punklibrarian/ATtiny_45_and_85_programmer_shield/KiCad/Version 1.2/ATtiny_45_and_85_programmer_shield.sch

## KiCad design KiCad/Version 1.2/ATtiny_45_and_85_programmer_shield.sch (2011-11-27)

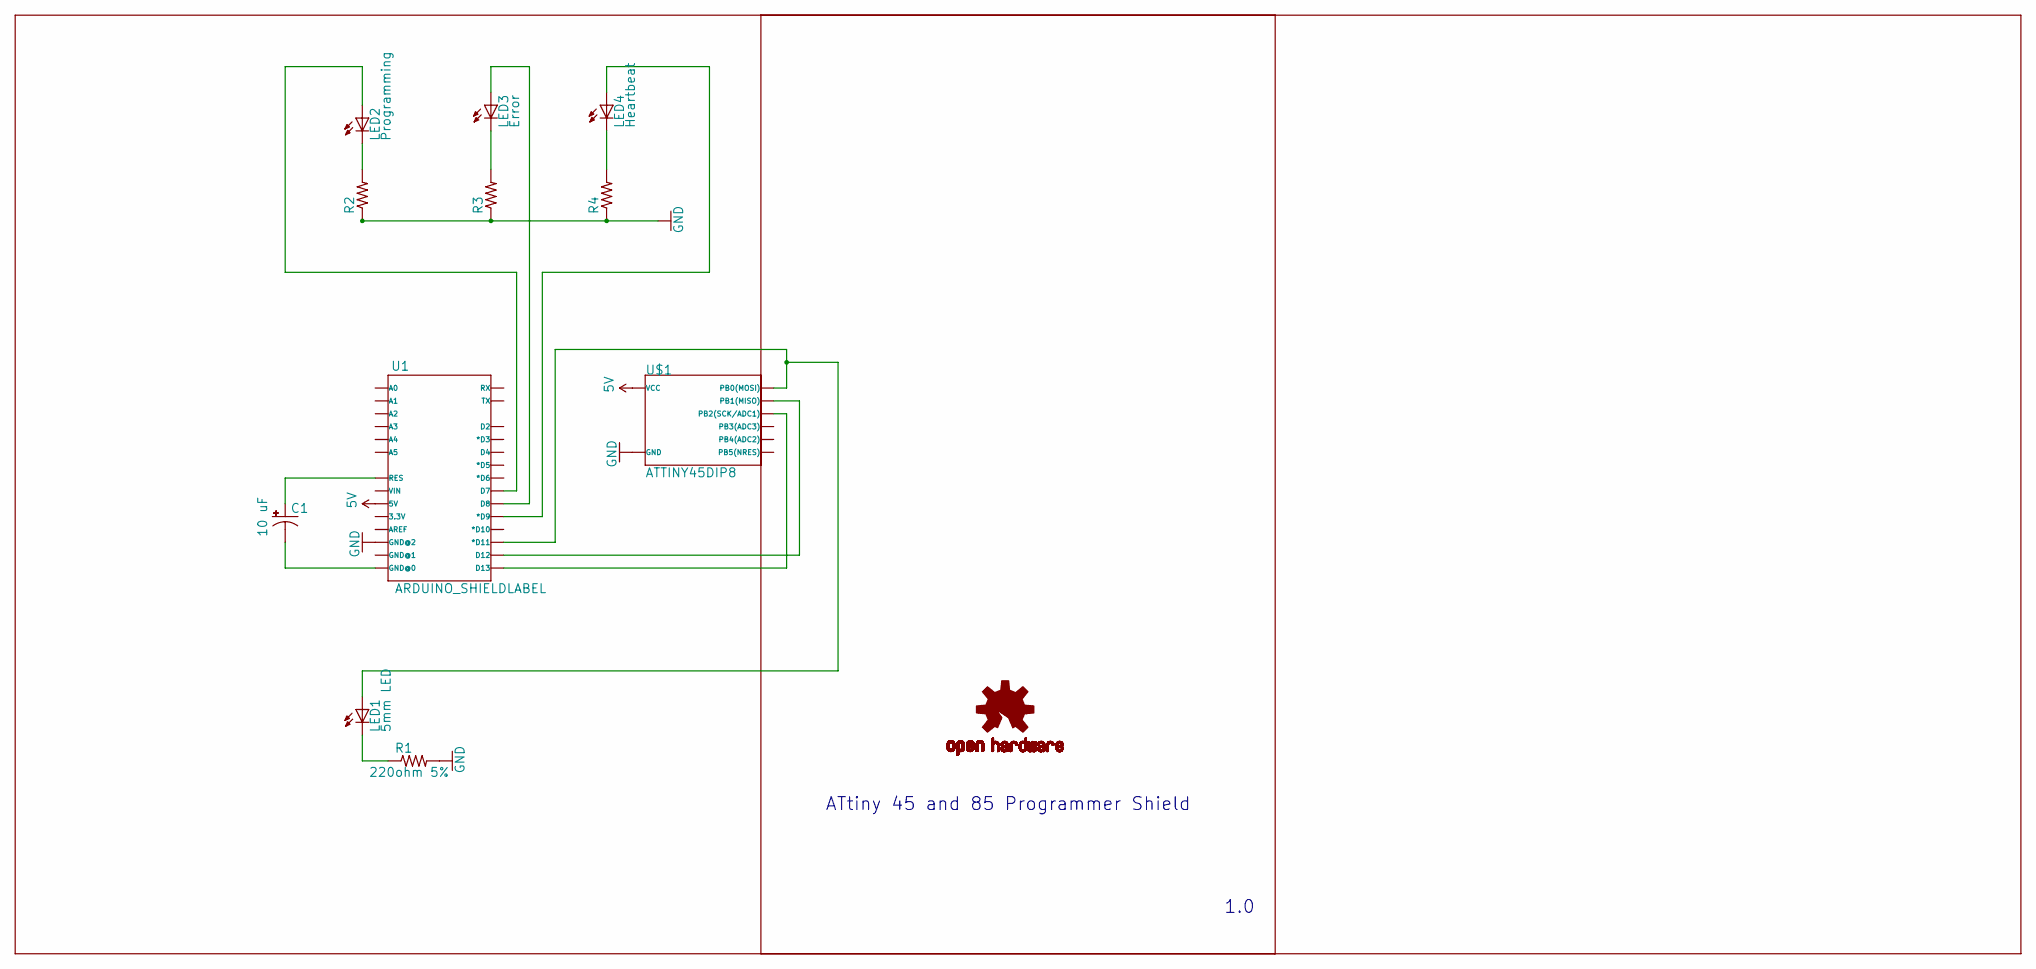
[picture p7: schematic ATtiny_45_and_85_programmer_shield.sch]

Parts:
C1: 10 uF
FRAME1: (no value)
GND1, GND2, GND3, GND4: (no value)
LED1: 5mm LED
LED2: Programming
LED3: Error
LED4: Heartbeat
R1: 220ohm 5%
R2, R3, R4: (no value)
U1: ARDUINO_SHIELDLABEL
U$1: U$1
U$2, U$3, U$4: (no value)

Connections:
unnamed: C1.A (+), U1.RES
unnamed: C1.C (-), U1.GND@0
unnamed: GND1.~, U1.GND@2
unnamed: GND2.~, U$1.4 (GND)
unnamed: GND3.~, R1.2
unnamed: GND4.~, R2.1, R3.1, R4.1
unnamed: LED1.A, U1.D11 (*D11), U$1.5 (PB0(MOSI))
unnamed: LED1.K (C), R1.1
unnamed: LED2.A, U1.D7
unnamed: LED2.K (C), R2.2
unnamed: LED3.A, U1.D8
unnamed: LED3.K (C), R3.2
unnamed: LED4.A, U1.D9 (*D9)
unnamed: LED4.K (C), R4.2
unnamed: U1.D12, U$1.6 (PB1(MISO))
unnamed: U1.D13, U$1.7 (PB2(SCK/ADC1))
unnamed: U$1.8 (VCC), U$2.~
unnamed: U1.5V, U$3.~

Notes on the sheet:
ATtiny 45 and 85 Programmer Shield
1.0
